Alexander-Komyakov/monopoly/photo1.jpg

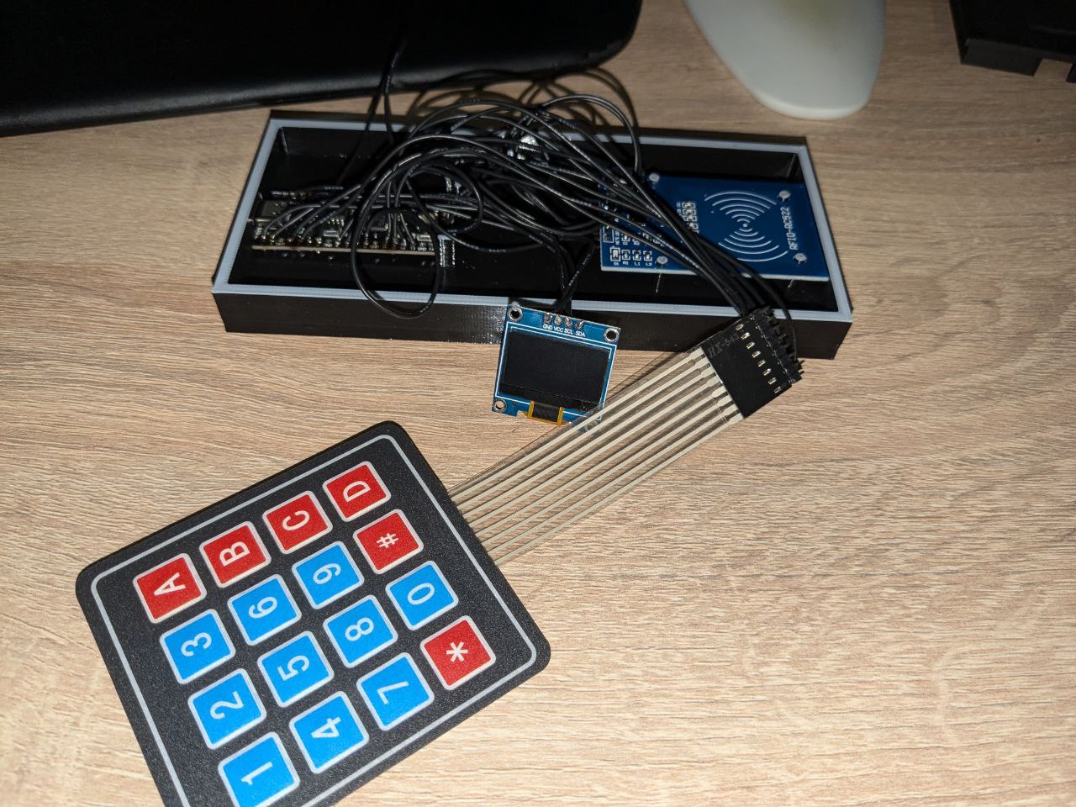
photo1.jpg
