Alexander-Komyakov/monopoly/photo2.jpg

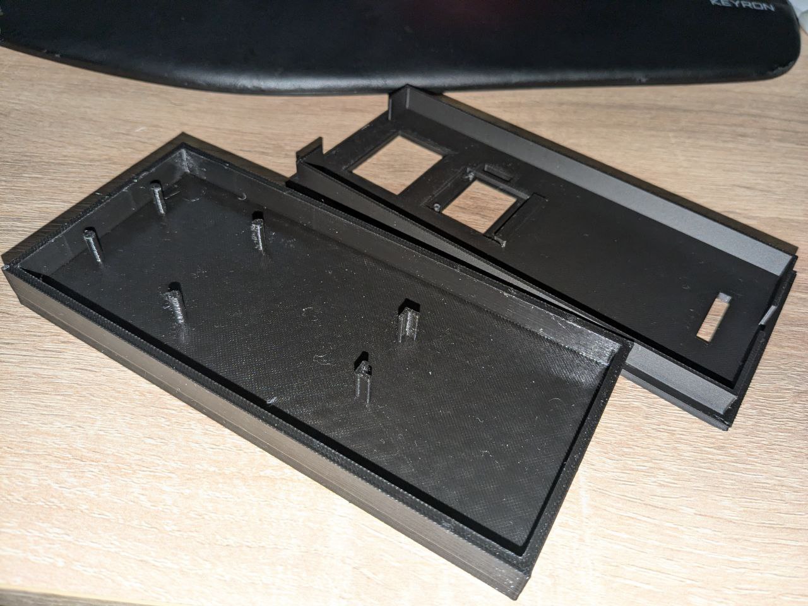
photo2.jpg
