Alexander-Komyakov/monopoly/photo3.jpg

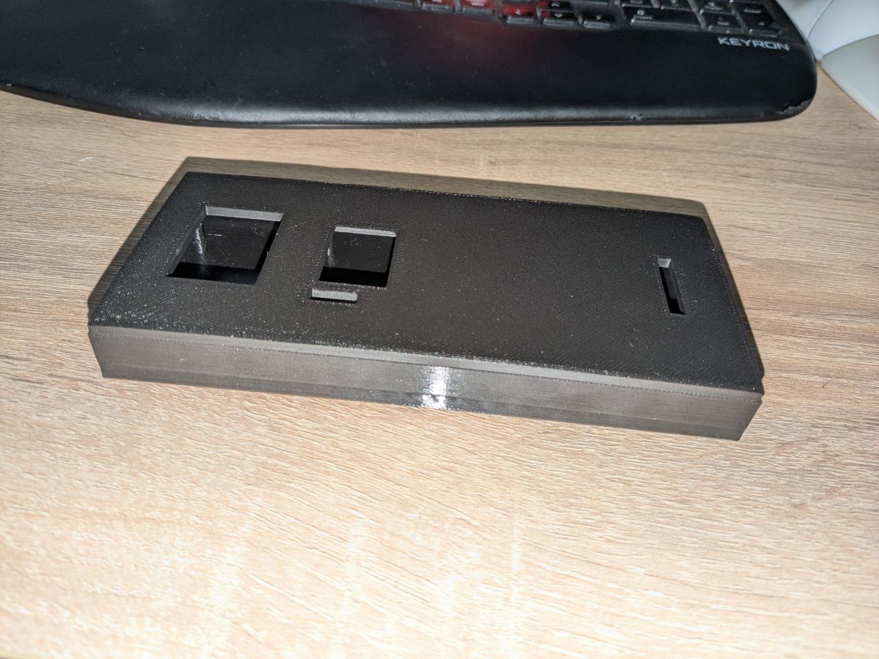
photo3.jpg
